iot-unimore/Auralys/docs/pics/wilson_head.png

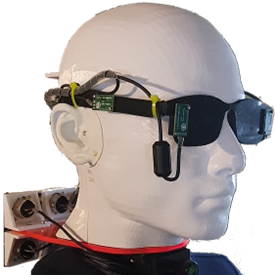
docs/pics/wilson_head.png
