iot-unimore/Auralys/hardware/motor_controller/motor_controller_BOT.jpg

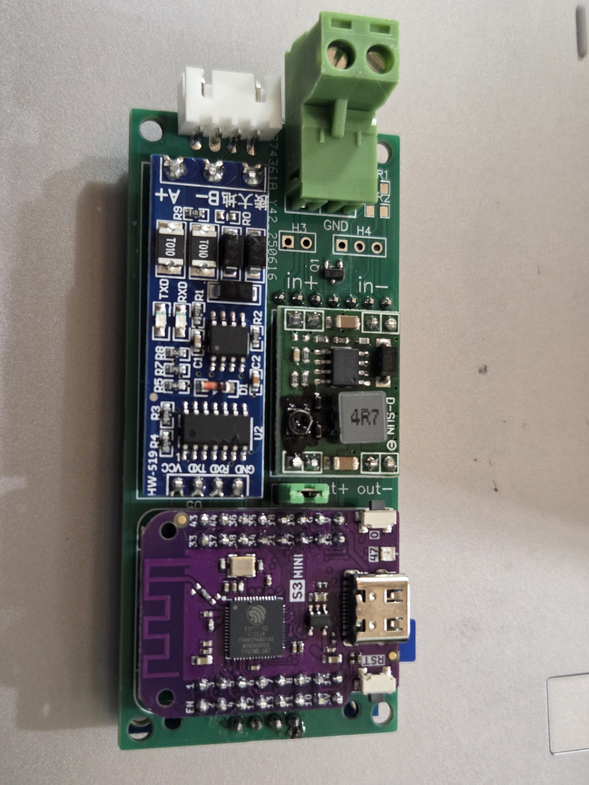
hardware/motor_controller/motor_controller_BOT.jpg
