iot-unimore/Auralys/hardware/motor_controller/motor_controller_TOP.jpg

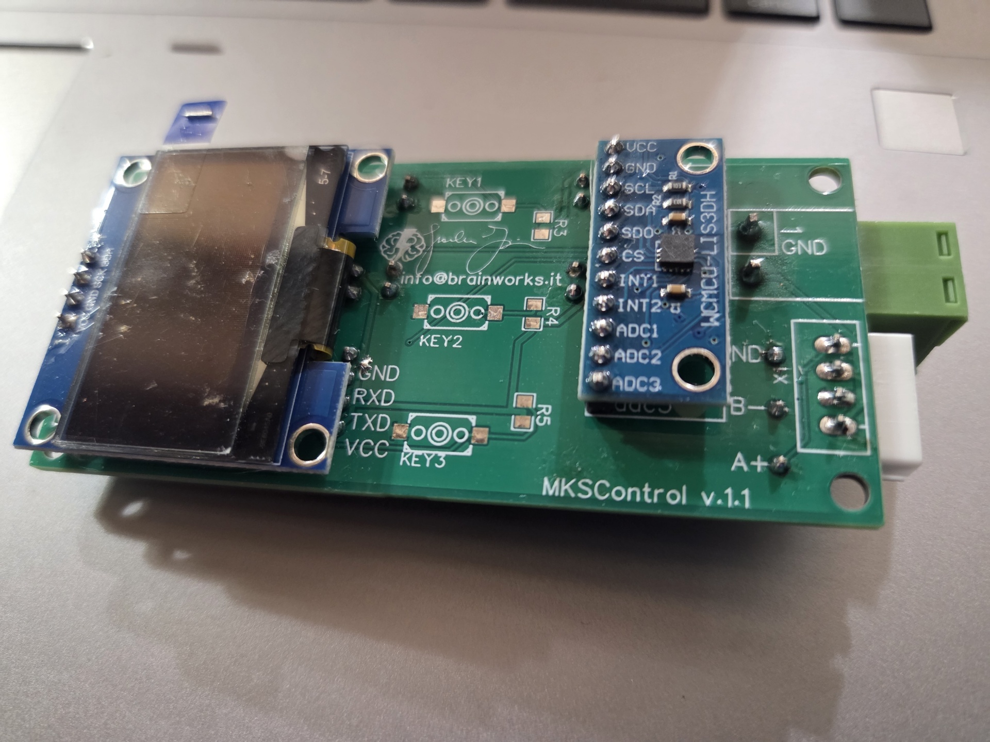
hardware/motor_controller/motor_controller_TOP.jpg
