iot-unimore/Auralys/hardware/OpenAural/body.png

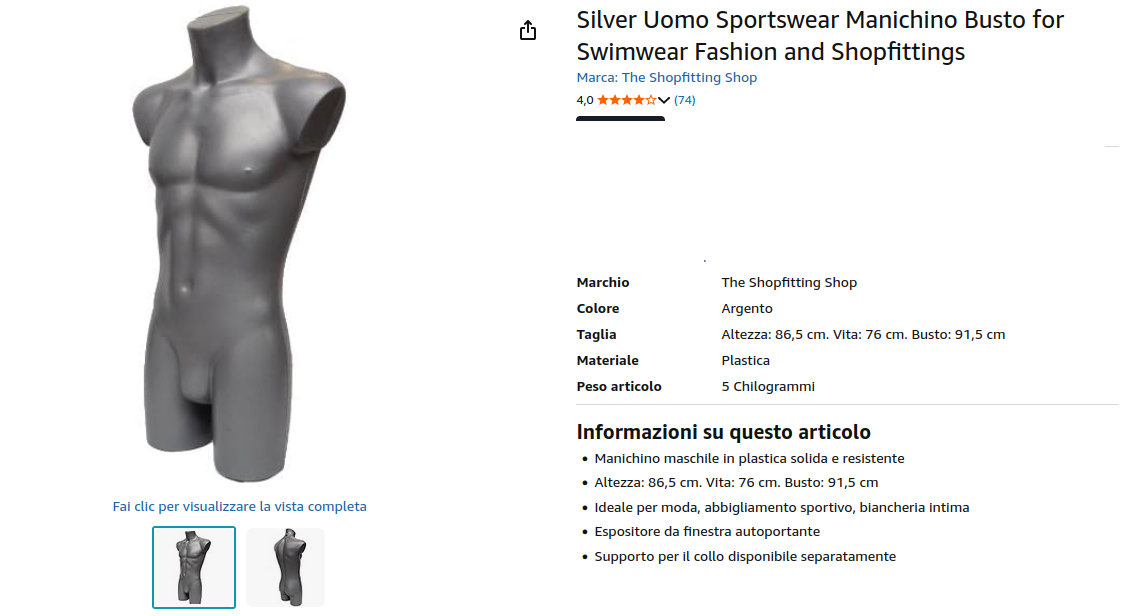
hardware/OpenAural/body.png
