iot-unimore/Auralys/hardware/rotating_table/stepper_motor/motor_gear.png

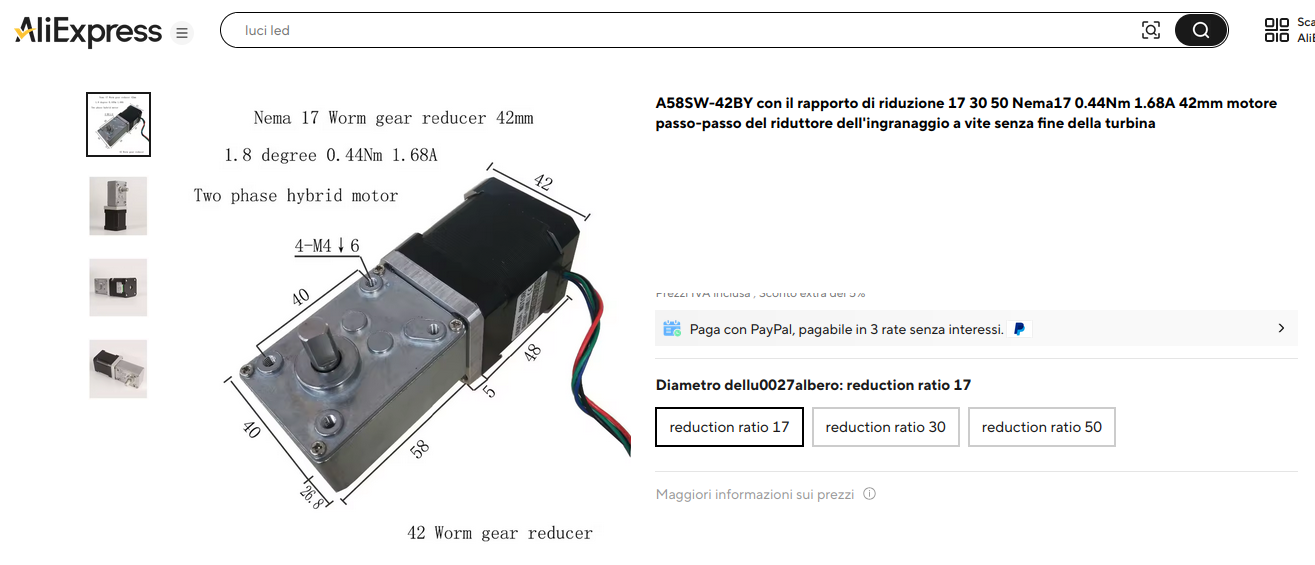
hardware/rotating_table/stepper_motor/motor_gear.png
