iot-unimore/Auralys/hardware/rotating_table/stepper_motor/motor_support/motor_support_full.png

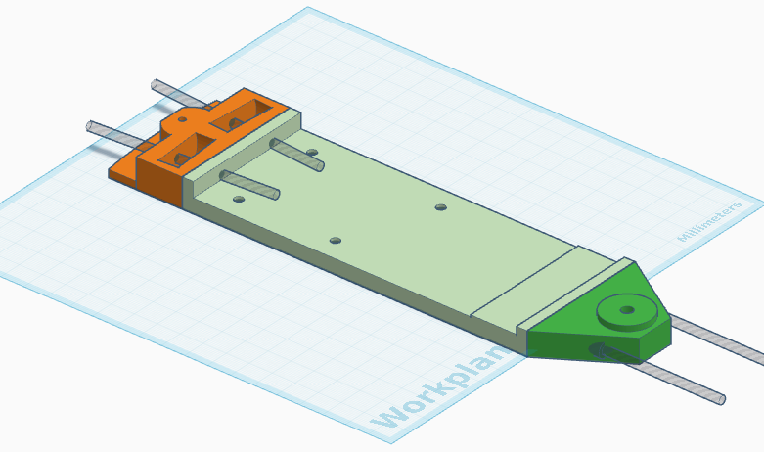
hardware/rotating_table/stepper_motor/motor_support/motor_support_full.png
