iot-unimore/Auralys/hardware/rotating_table/stepper_motor/spurgear_rtable.png

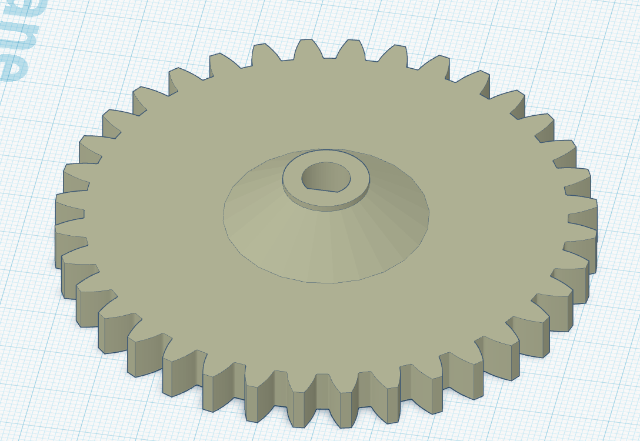
hardware/rotating_table/stepper_motor/spurgear_rtable.png
