iot-unimore/Auralys/hardware/standing_poles/stepper_motor/mks_servo57D.png

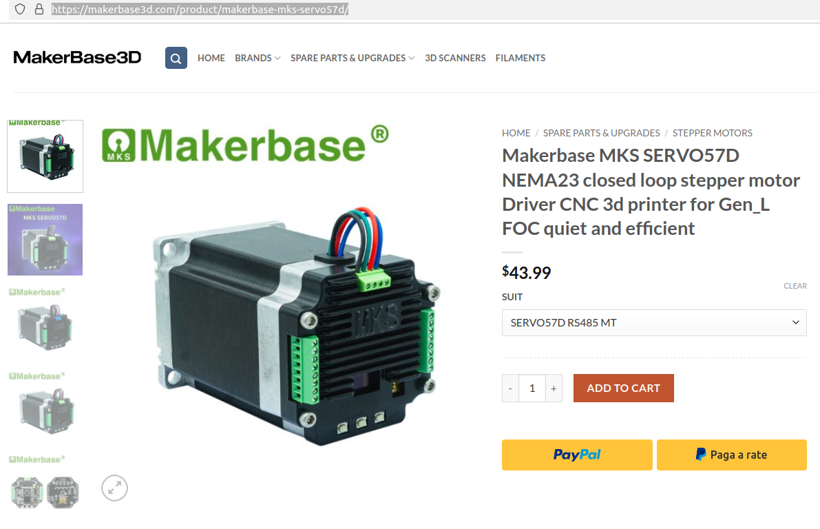
hardware/standing_poles/stepper_motor/mks_servo57D.png
