iot-unimore/Auralys/hardware/motor_controller/parts_list/display_i2c_1.3inch.png

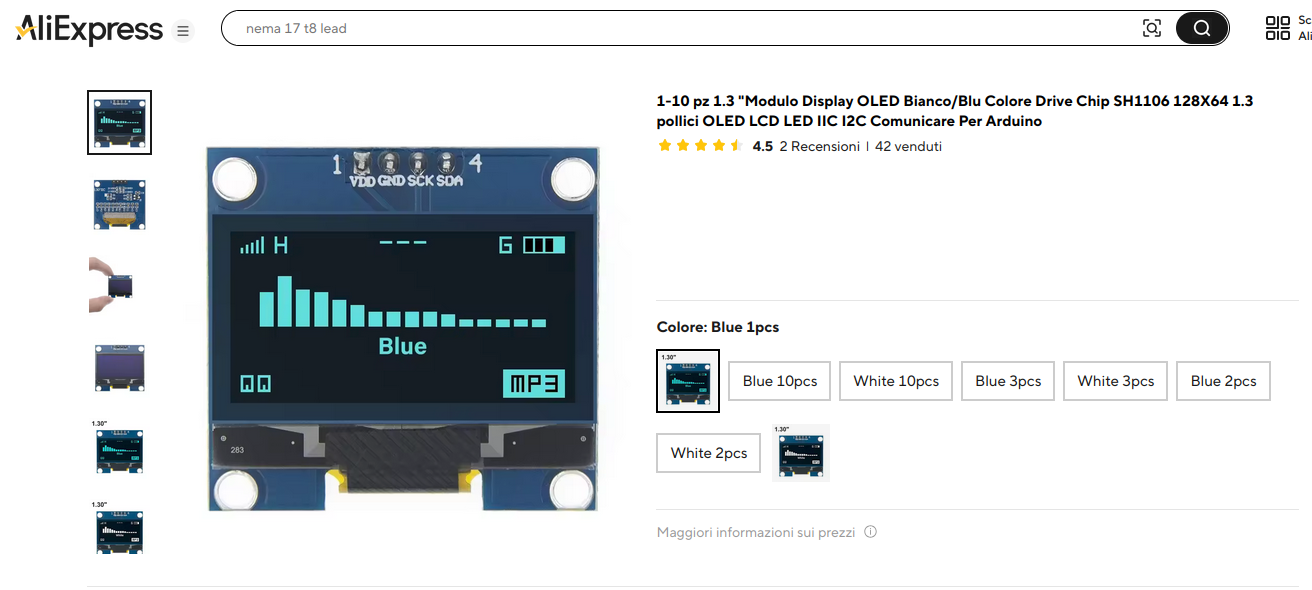
hardware/motor_controller/parts_list/display_i2c_1.3inch.png
