iot-unimore/Auralys/hardware/motor_controller/parts_list/lolin_esp32-s3_mini.png

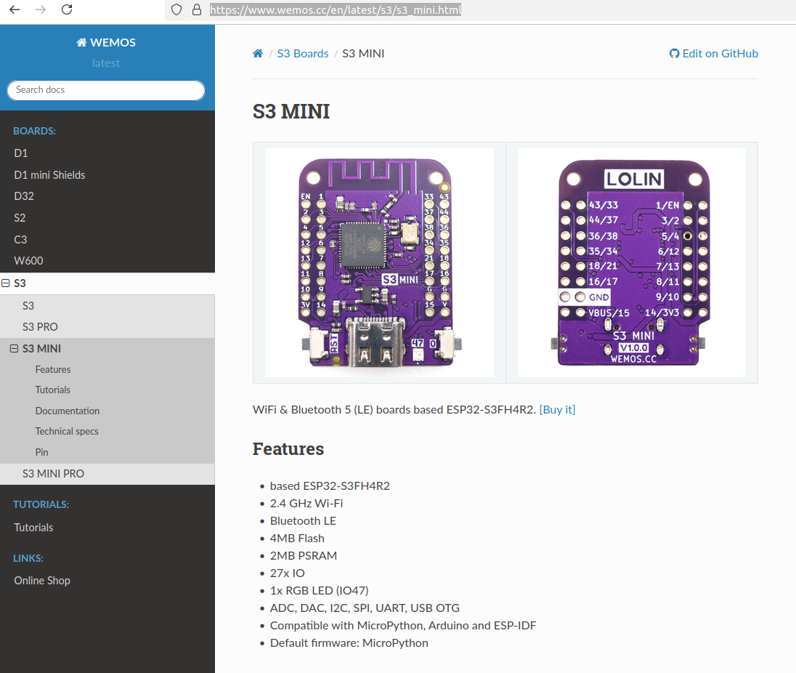
hardware/motor_controller/parts_list/lolin_esp32-s3_mini.png
