iot-unimore/Auralys/hardware/motor_controller/parts_list/motion_LIS-3DSH.png

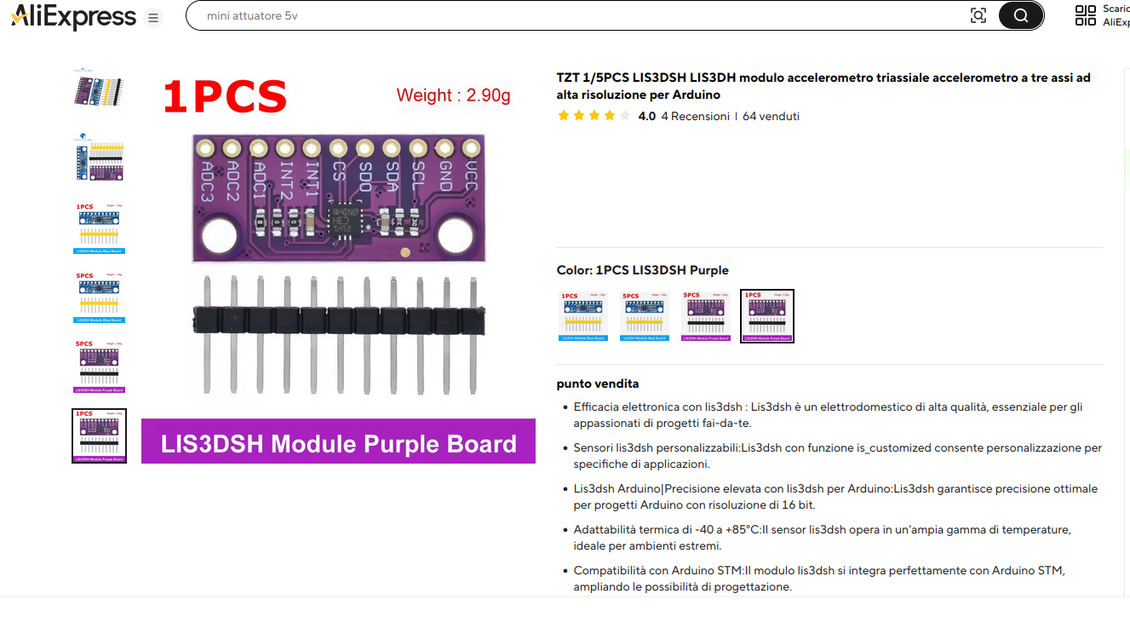
hardware/motor_controller/parts_list/motion_LIS-3DSH.png
