iot-unimore/Auralys/hardware/motor_controller/parts_list/serial_to_485_HW-519.png

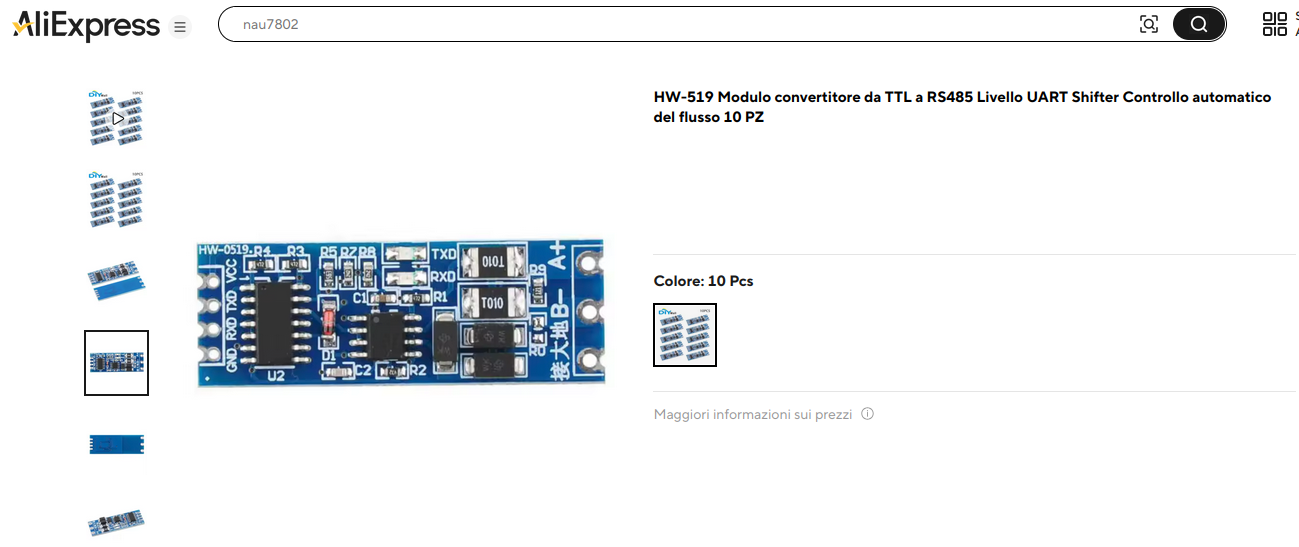
hardware/motor_controller/parts_list/serial_to_485_HW-519.png
