iot-unimore/Auralys/hardware/rotating_table/bot_square_table/parts_list/center_shaft_bearing.png

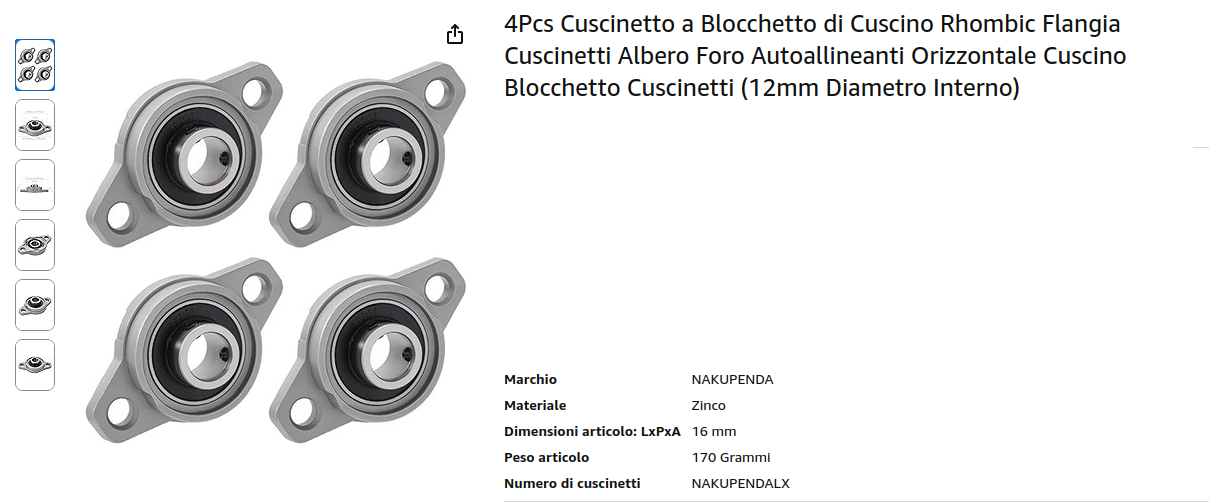
hardware/rotating_table/bot_square_table/parts_list/center_shaft_bearing.png
