iot-unimore/Auralys/hardware/rotating_table/top_round_table/parts_list/center_shaft_flange.png

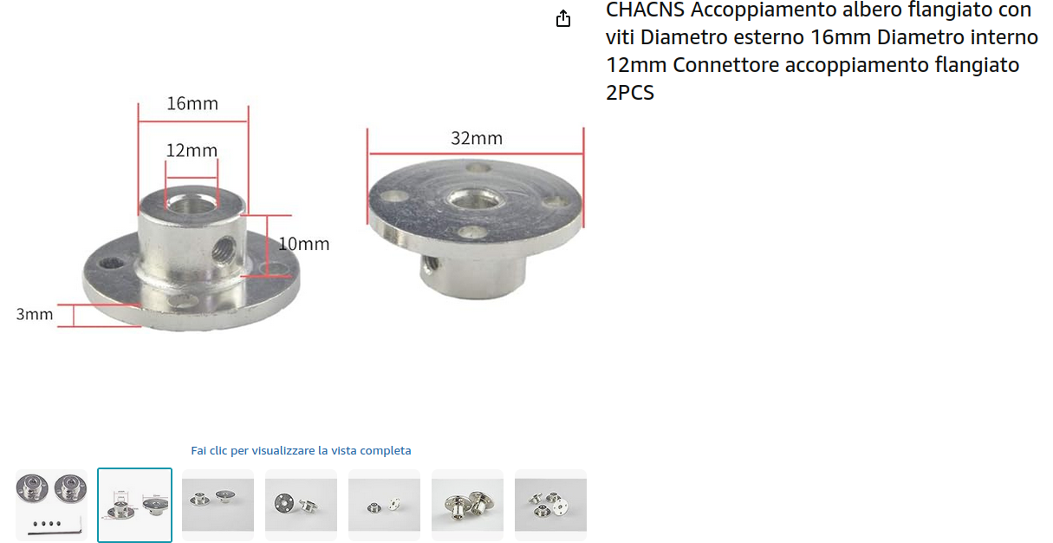
hardware/rotating_table/top_round_table/parts_list/center_shaft_flange.png
