iot-unimore/Auralys/hardware/rotating_table/top_round_table/parts_list/center_shaft_flange_extension.png

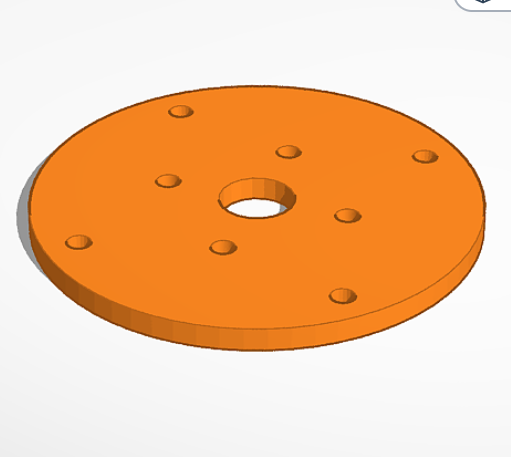
hardware/rotating_table/top_round_table/parts_list/center_shaft_flange_extension.png
