iot-unimore/Auralys/hardware/rotating_table/top_round_table/parts_list/spurgear_90cm_element_x4.png

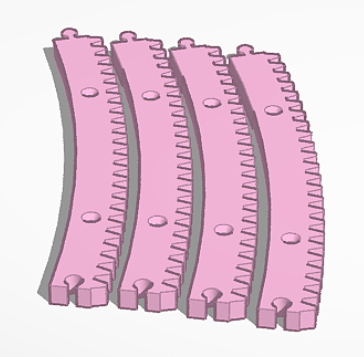
hardware/rotating_table/top_round_table/parts_list/spurgear_90cm_element_x4.png
