iot-unimore/Auralys/hardware/rotating_table/top_round_table/parts_list/wheels_76mm_skateboard.png

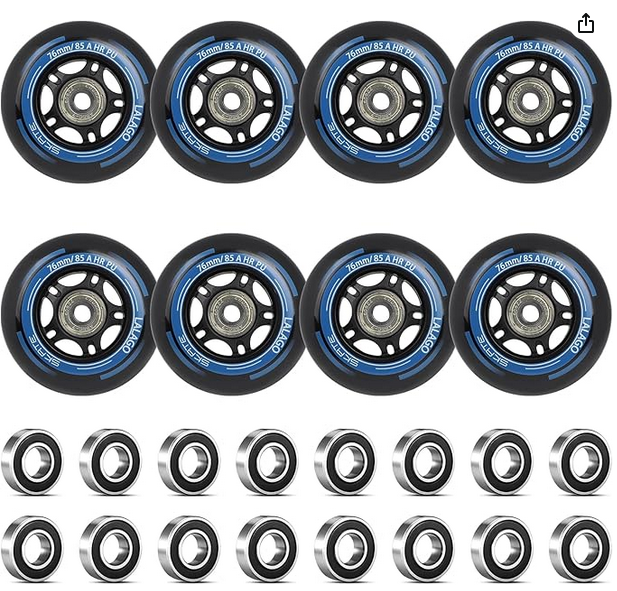
hardware/rotating_table/top_round_table/parts_list/wheels_76mm_skateboard.png
