iot-unimore/Auralys/hardware/speaker/case/part_list/auralys_speaker_ikea_bowl.png

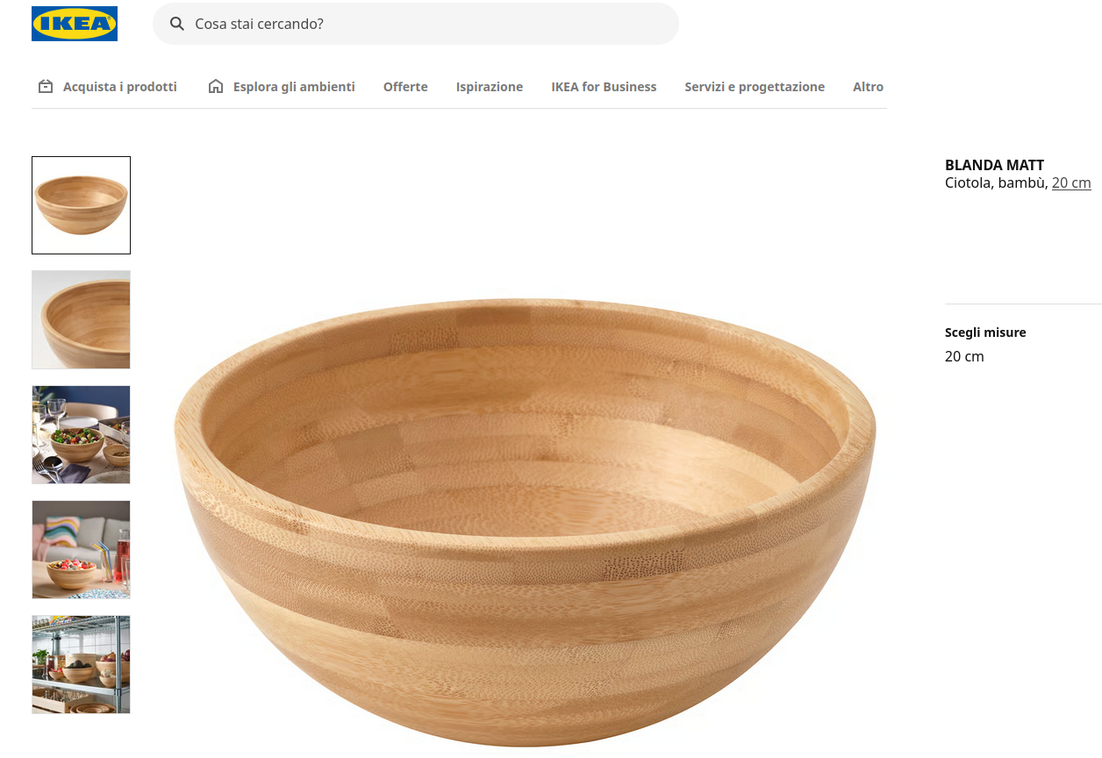
hardware/speaker/case/part_list/auralys_speaker_ikea_bowl.png
