iot-unimore/Auralys/hardware/speaker/gimbal/part_list/ball_bearing.png

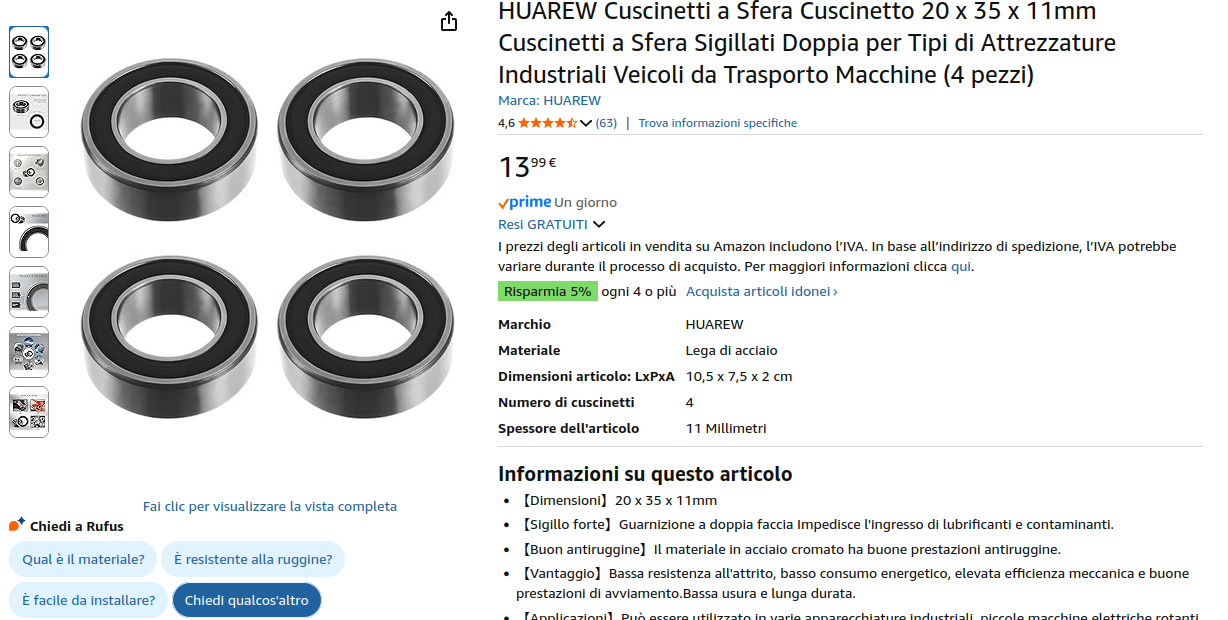
hardware/speaker/gimbal/part_list/ball_bearing.png
