iot-unimore/Auralys/hardware/speaker/gimbal/part_list/nema_stepper_motor.png

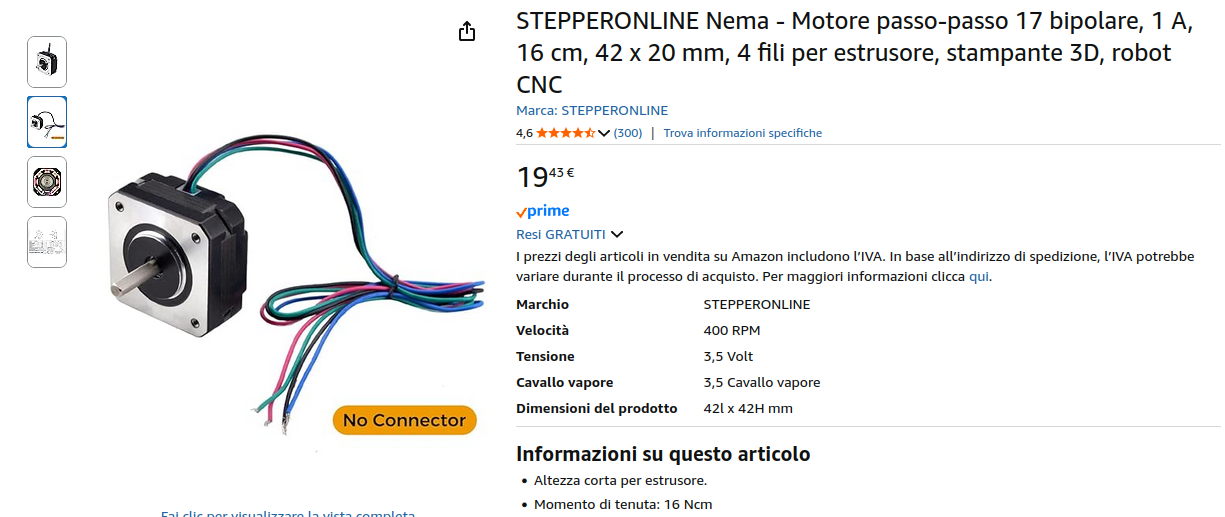
hardware/speaker/gimbal/part_list/nema_stepper_motor.png
