iot-unimore/Auralys/hardware/standing_poles/parts_list/plate.png

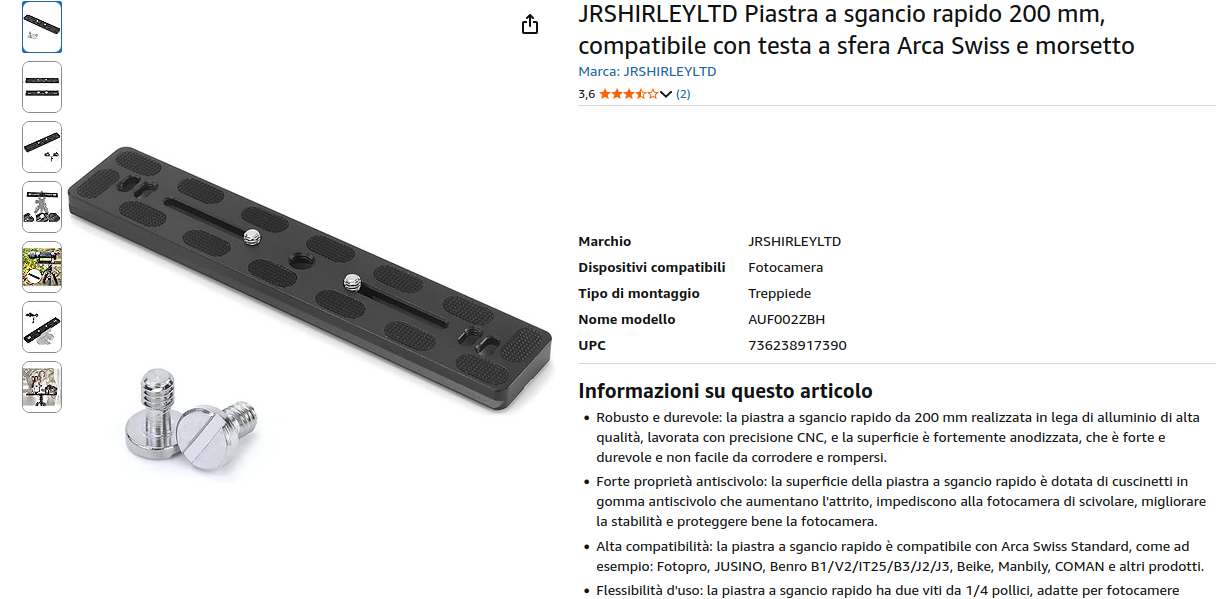
hardware/standing_poles/parts_list/plate.png
