iot-unimore/Auralys/hardware/standing_poles/parts_list/plate_holder.png

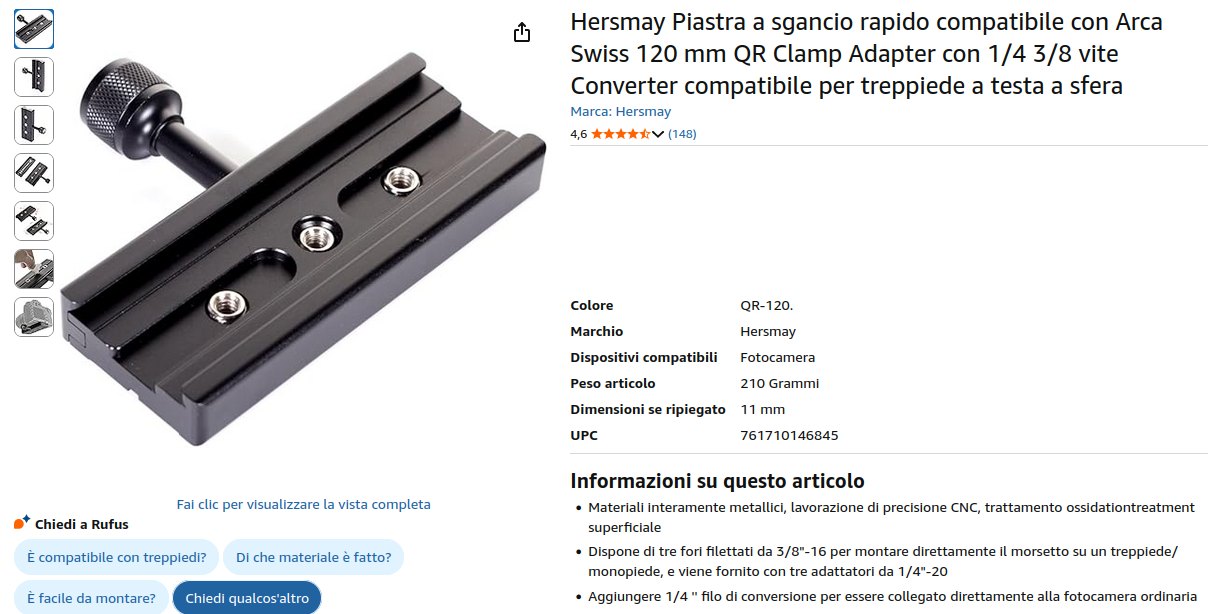
hardware/standing_poles/parts_list/plate_holder.png
