iot-unimore/Auralys/hardware/standing_poles/parts_list/standing_pole.png

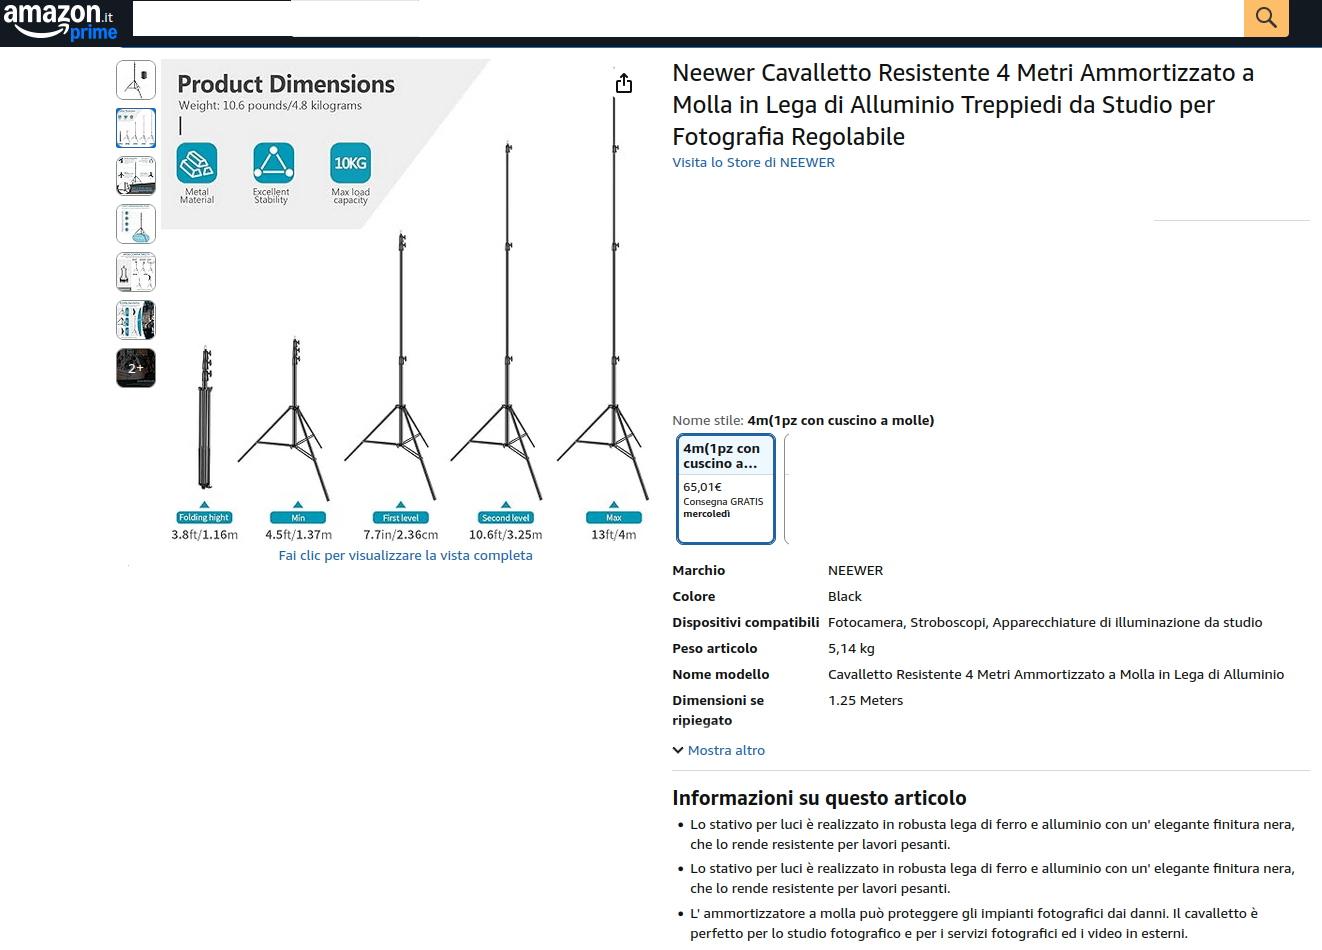
hardware/standing_poles/parts_list/standing_pole.png
