iot-unimore/Auralys/hardware/standing_poles/parts_list/suspension_wire.png

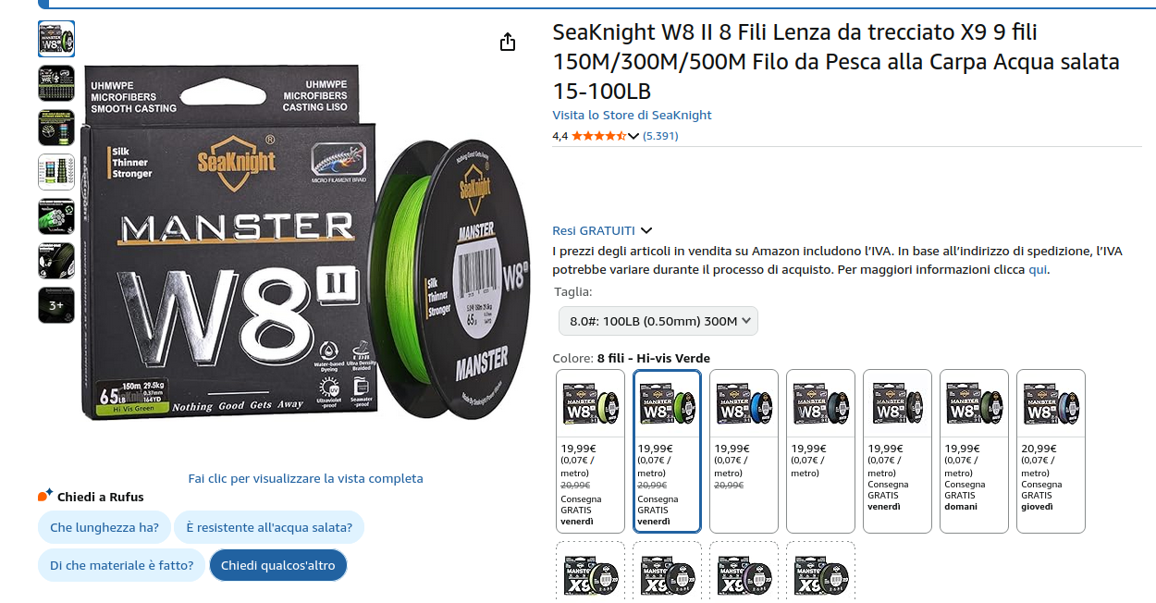
hardware/standing_poles/parts_list/suspension_wire.png
