iot-unimore/Auralys/hardware/OpenAural/Ear_right.stl

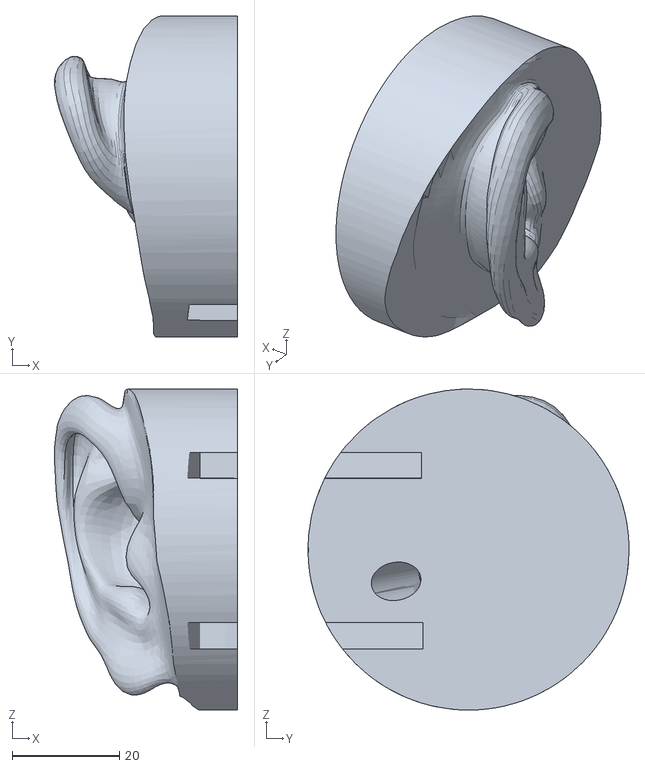
[picture p51: CAD file, 2025-10-20]
hardware/OpenAural/Ear_right.stl
34.2 x 60.0 x 60.0
