iot-unimore/Auralys/hardware/rotating_table/stepper_motor/motor_support/MKS_RTable_base.stl

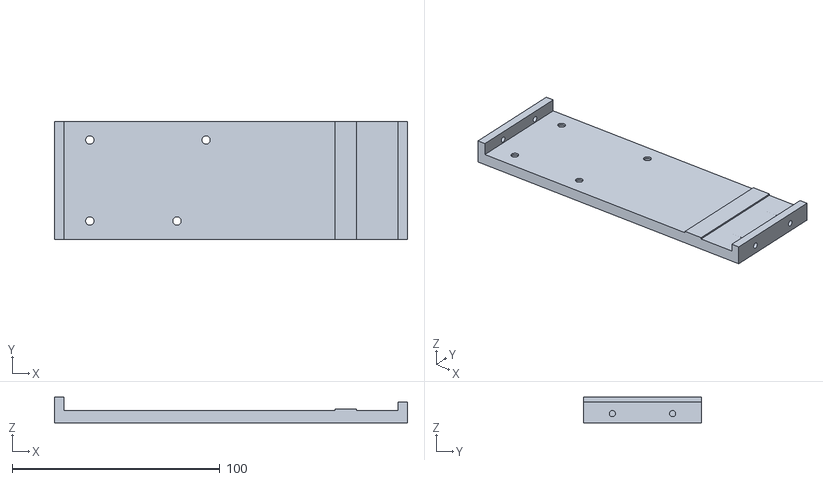
[picture p52: CAD file, 2026-09-18]
hardware/rotating_table/stepper_motor/motor_support/MKS_RTable_base.stl
170.0 x 57.0 x 12.5
