iot-unimore/Auralys/hardware/rotating_table/top_round_table/parts_list/spurgear_90cm_element_x4.stl

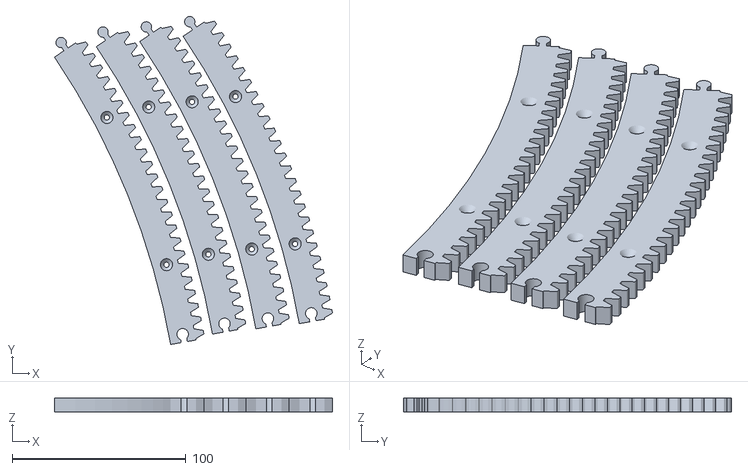
[picture p53: CAD file, 2025-10-12]
hardware/rotating_table/top_round_table/parts_list/spurgear_90cm_element_x4.stl
160.2 x 189.0 x 8.00
