iot-unimore/Auralys/hardware/speaker/gimbal/gimbal_plate.stl

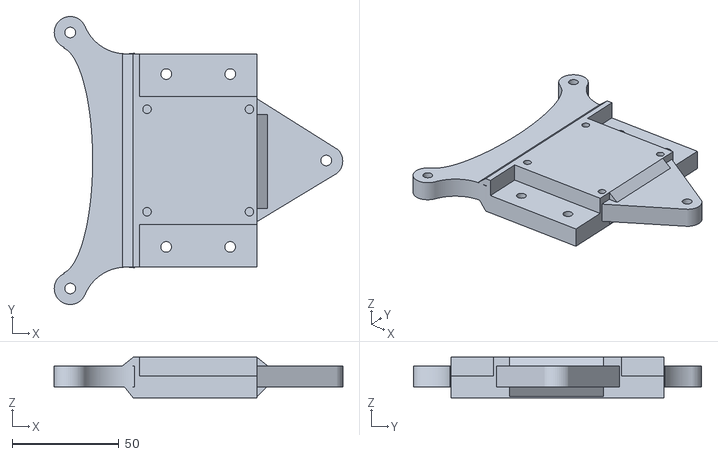
[picture p54: CAD file, 2025-10-20]
hardware/speaker/gimbal/gimbal_plate.stl
135.3 x 135.0 x 19.0
