iot-unimore/Auralys/hardware/standing_poles/stepper_motor/mks_9cm_spool.stl

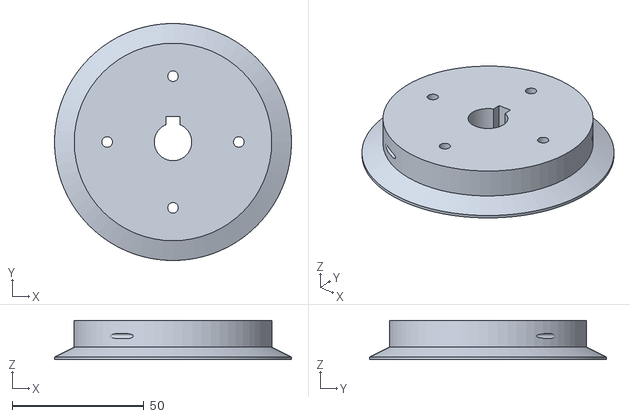
[picture p55: CAD file, 2025-10-20]
hardware/standing_poles/stepper_motor/mks_9cm_spool.stl
90.0 x 90.0 x 15.0
