iot-unimore/Auralys/hardware/standing_poles/wire_wheel/mks_wire_holder_wheel.stl

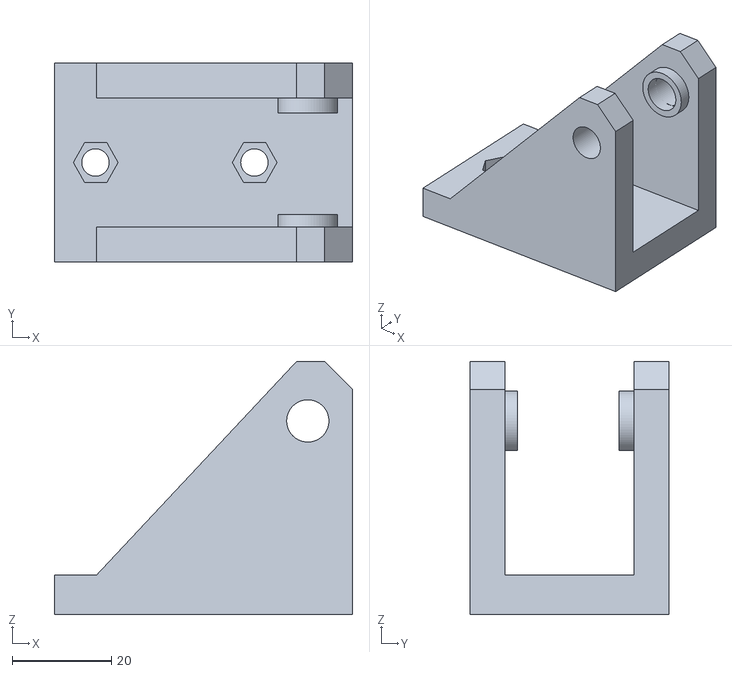
[picture p56: CAD file, 2025-10-20]
hardware/standing_poles/wire_wheel/mks_wire_holder_wheel.stl
60.0 x 40.0 x 51.0
