iot-unimore/Auralys/hardware/rotating_table/stepper_motor/motor_support/MKS_RTable_wheels-3.stl

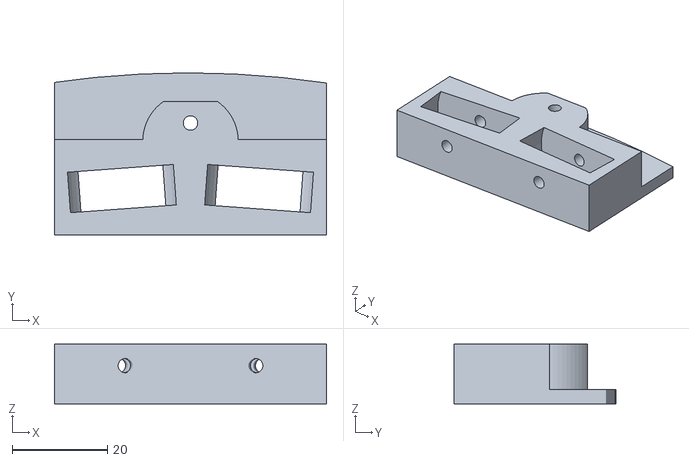
[picture p57: CAD file, 2025-10-20]
hardware/rotating_table/stepper_motor/motor_support/MKS_RTable_wheels-3.stl
57.0 x 34.0 x 12.5
