iot-unimore/Auralys/hardware/speaker/gimbal/gimbal_side.stl

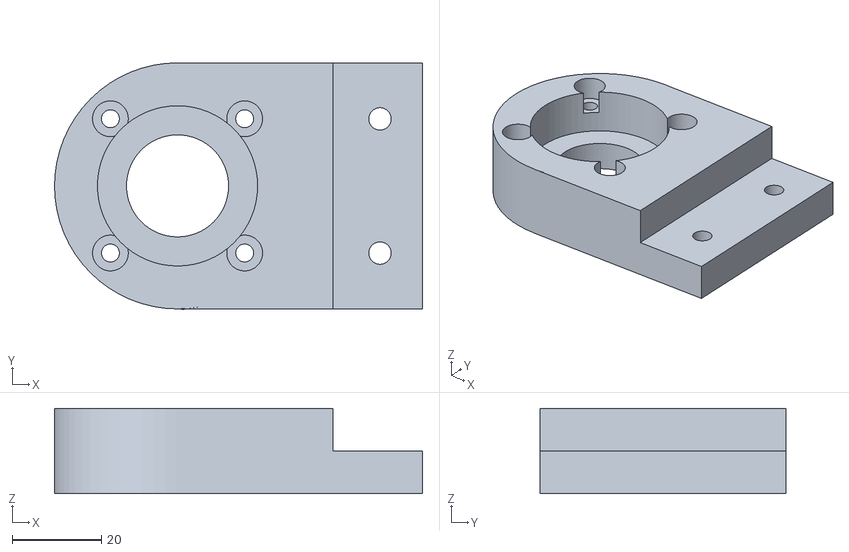
[picture p58: CAD file, 2025-10-20]
hardware/speaker/gimbal/gimbal_side.stl
82.2 x 55.1 x 19.0
