iot-unimore/Auralys/hardware/rotating_table/stepper_motor/motor_support/MKS_support_plate.stl

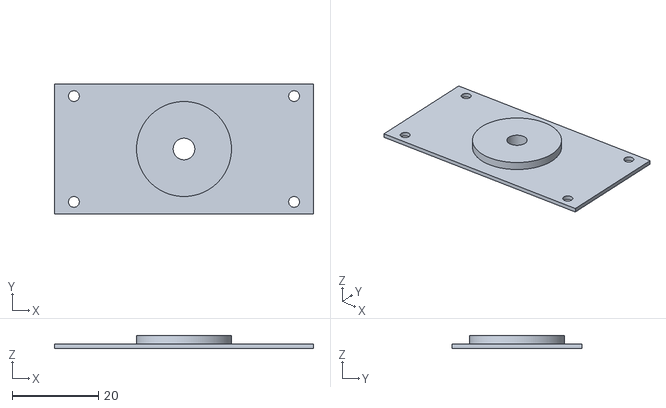
[picture p59: CAD file, 2025-10-20]
hardware/rotating_table/stepper_motor/motor_support/MKS_support_plate.stl
60.0 x 30.0 x 3.00
