iot-unimore/Auralys/hardware/speaker/gimbal/gimbal_curve.stl

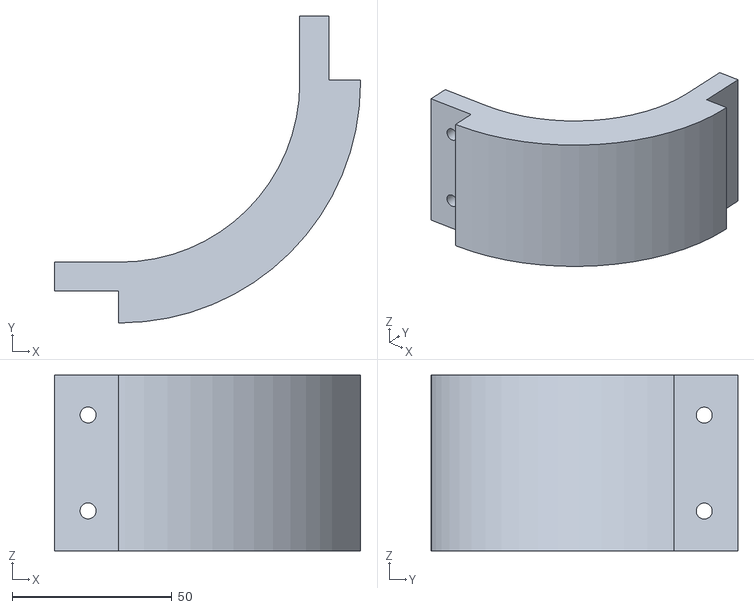
[picture p60: CAD file, 2025-10-20]
hardware/speaker/gimbal/gimbal_curve.stl
95.7 x 95.9 x 55.0
