iot-unimore/Auralys/hardware/OpenAural/Head_back.STL

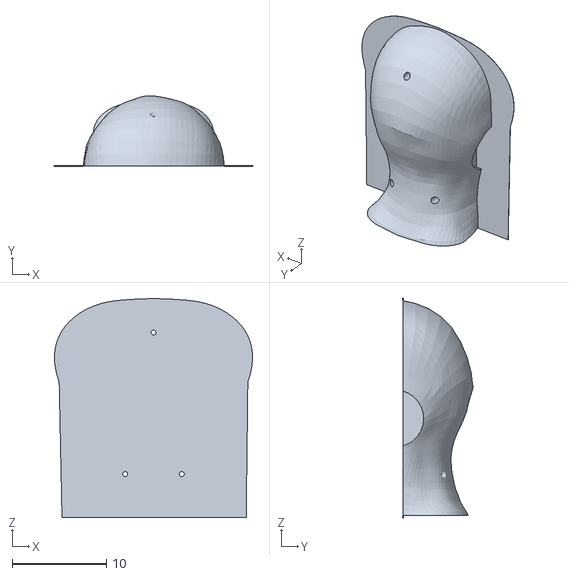
[picture p61: CAD file, 2025-10-20]
hardware/OpenAural/Head_back.STL
21.0 x 7.44 x 23.2
