iot-unimore/Auralys/hardware/rotating_table/stepper_motor/motor_support/MKS_RTable_perno.stl

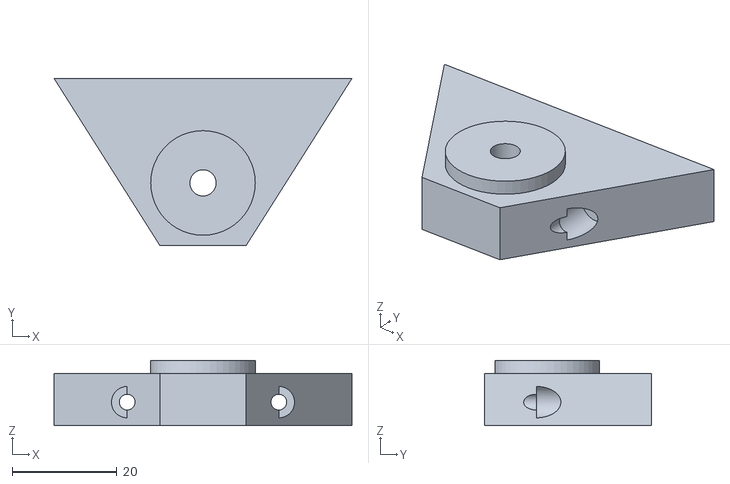
[picture p62: CAD file, 2025-10-20]
hardware/rotating_table/stepper_motor/motor_support/MKS_RTable_perno.stl
57.0 x 32.0 x 12.5
