iot-unimore/Auralys/hardware/rotating_table/stepper_motor/motor_support/MKS_holder.stl

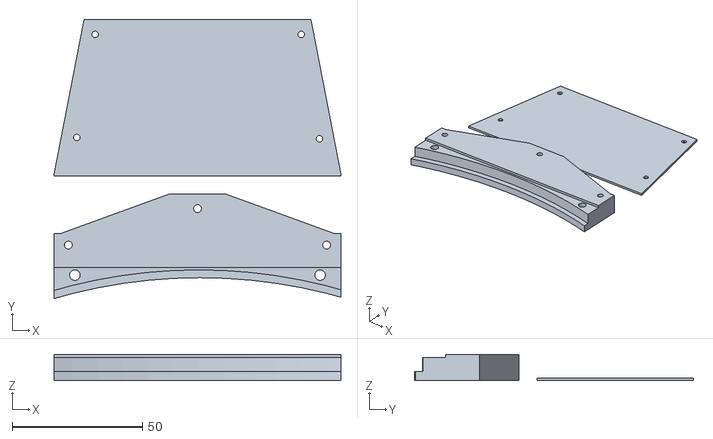
[picture p63: CAD file, 2025-10-20]
hardware/rotating_table/stepper_motor/motor_support/MKS_holder.stl
110.0 x 107.0 x 10.0
