iot-unimore/Auralys/hardware/motor_controller/parts_list/step_down_dc-dc_MPS1584.png

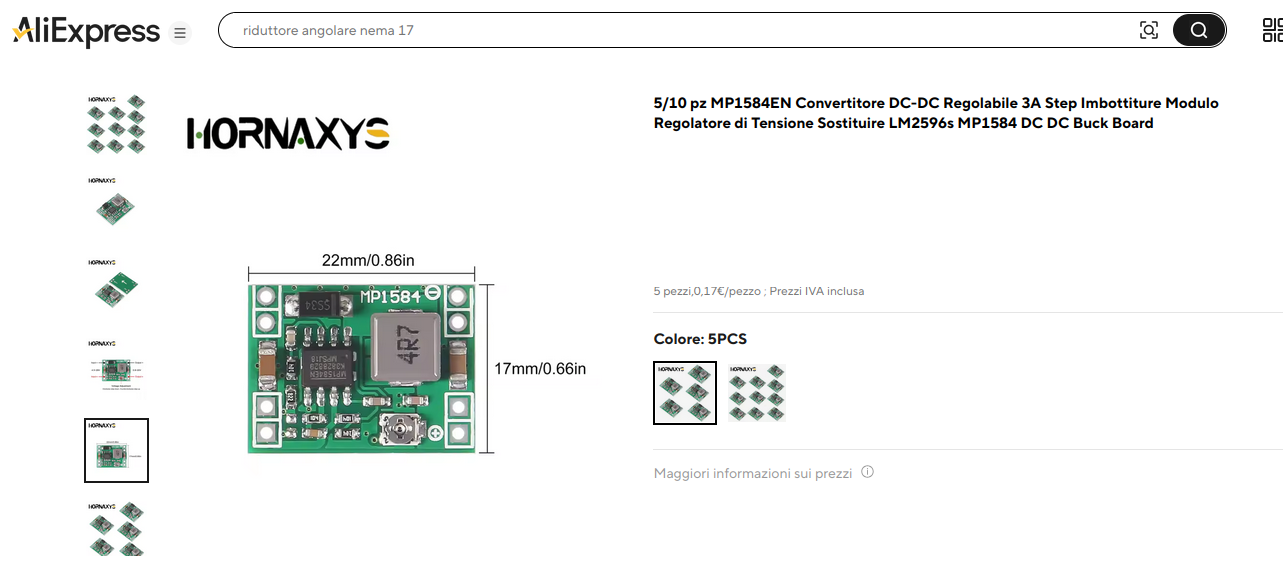
hardware/motor_controller/parts_list/step_down_dc-dc_MPS1584.png
