iot-unimore/Auralys/hardware/speaker/auralys_speaker_assembly_01.png

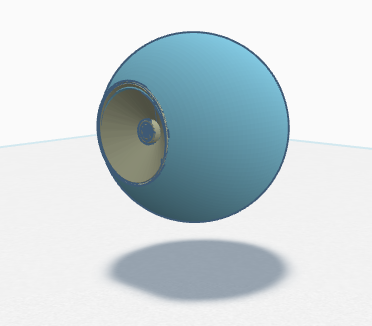
hardware/speaker/auralys_speaker_assembly_01.png
