iot-unimore/Auralys/hardware/speaker/auralys_speaker_assembly_02.png

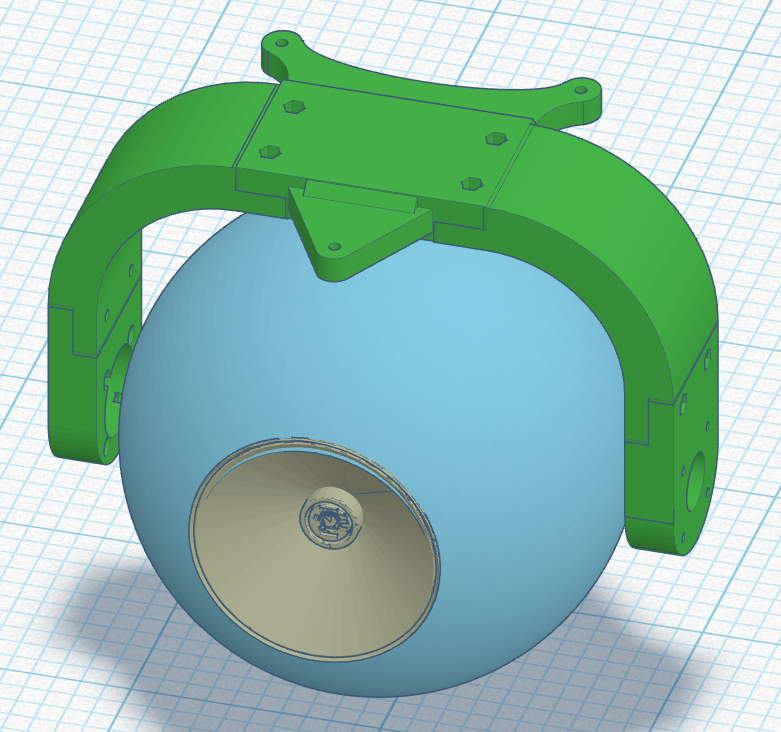
hardware/speaker/auralys_speaker_assembly_02.png
